sschuchman/thorCam/3D_Models/images/tension/Screenshot 2024-08-27 at 11.53.31 AM.png

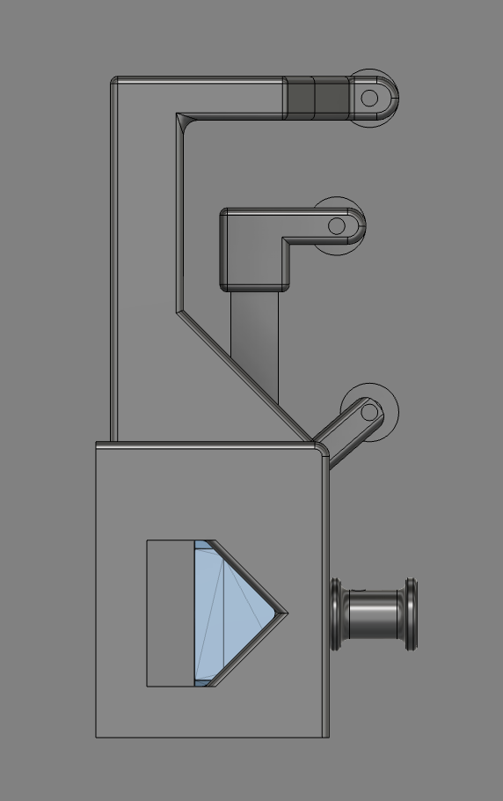
3D_Models/images/tension/Screenshot 2024-08-27 at 11.53.31 AM.png
